re-innovation/gridMeter/Software/gridMeter/indicator.h

#ifndef _INDICATOR_H_
#define _INDICATOR_H_

// Sets how far the indicator can travel (units of frequency * 1000)
static const uint16_t MIN_FREQ_LIMIT = 49900;
static const uint16_t MAX_FREQ_LIMIT = 50100;

void indicator_setup();
void indicator_home();
int indicator_moveto_freq(uint16_t freq, uint16_t timer);
void indicator_moveto_freq_blocking(uint16_t freq);
void indicator_tick(uint16_t timer);

#endif
